jimmyng94/PawBeat/Other/Media/BPM.png

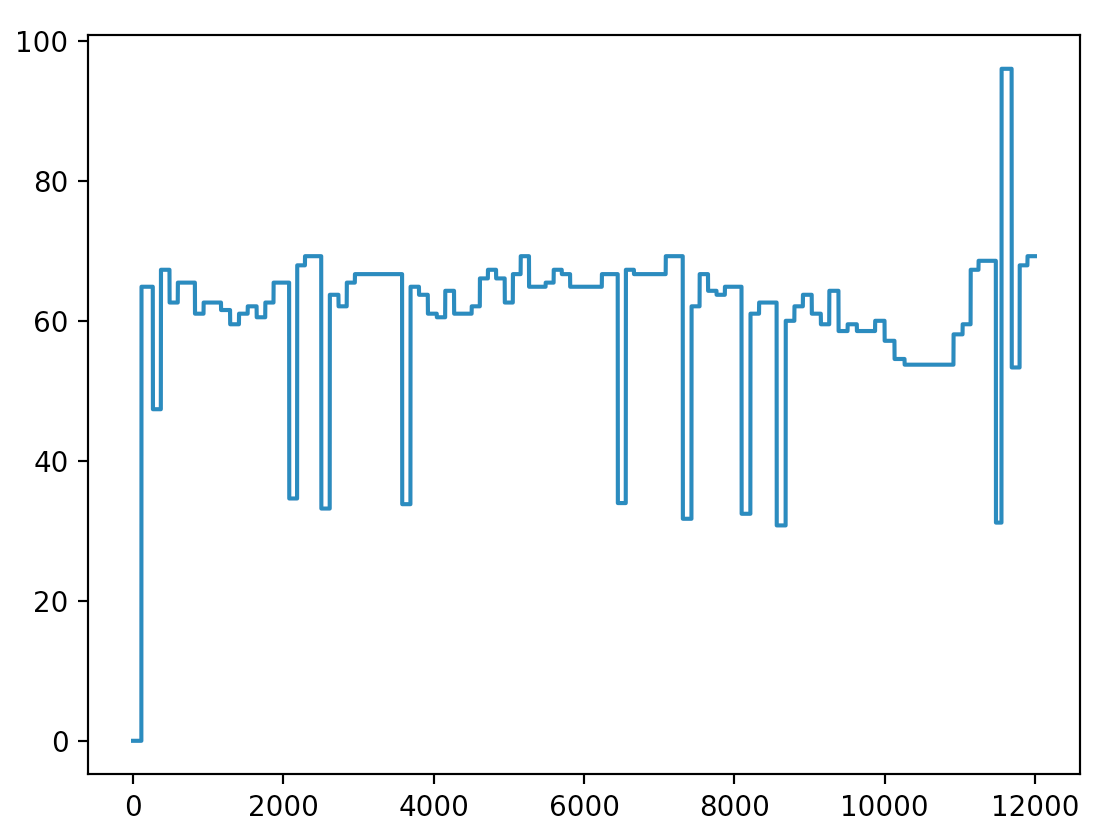
Other/Media/BPM.png
