jimmyng94/PawBeat/Other/Media/Filtered Data.png

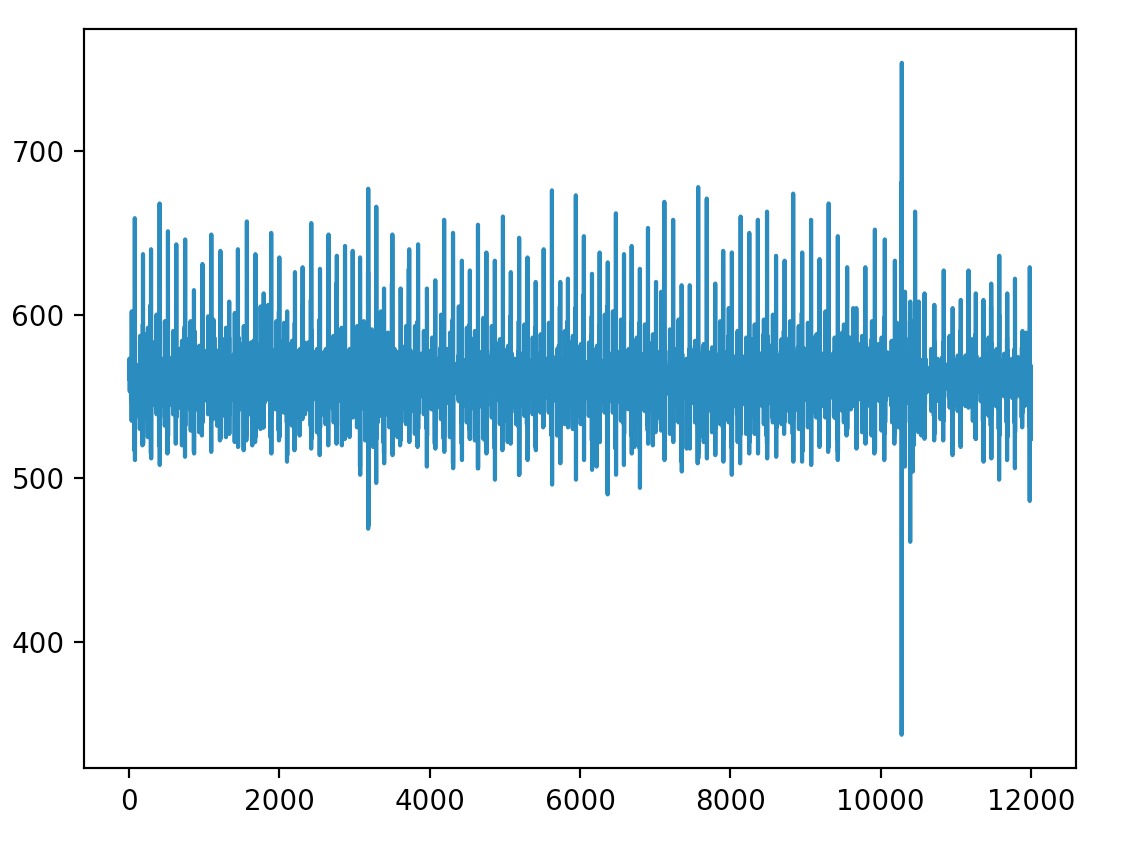
Other/Media/Filtered Data.png
