jimmyng94/PawBeat/Other/Media/Filtered_Zoom.png

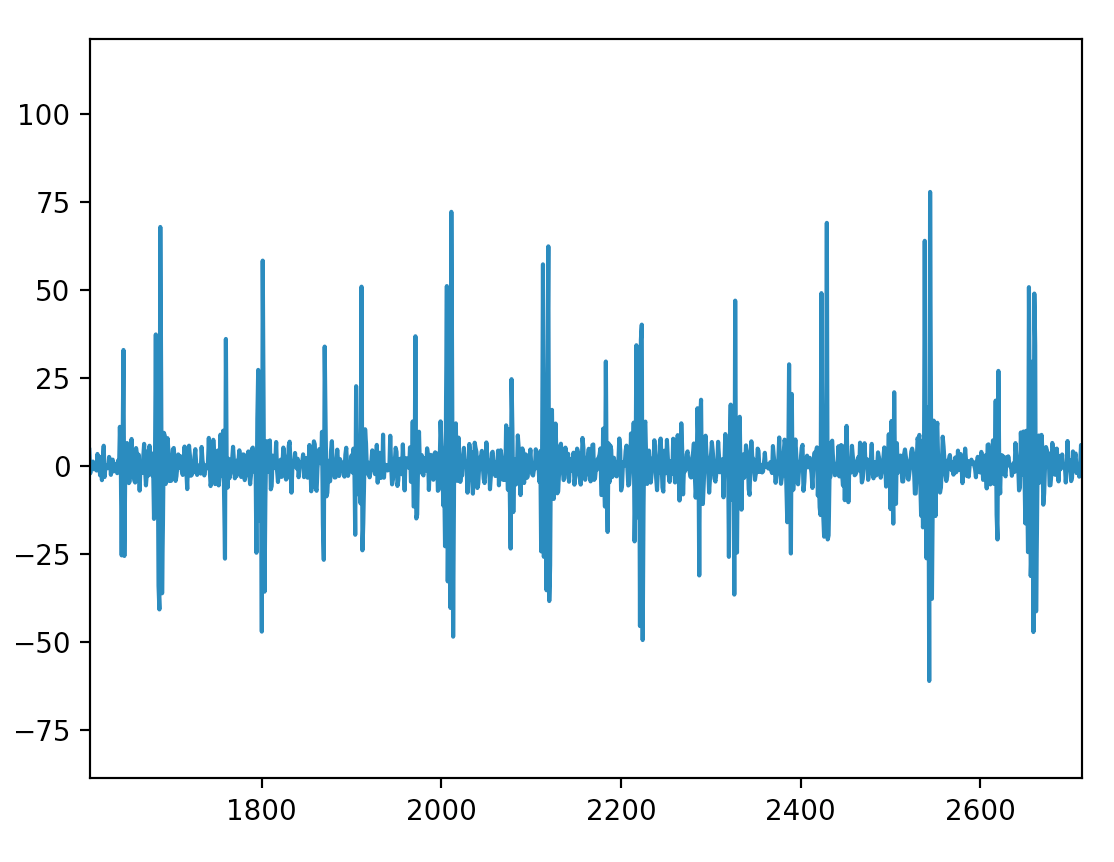
Other/Media/Filtered_Zoom.png
