jimmyng94/PawBeat/Other/Media/image0.jpeg

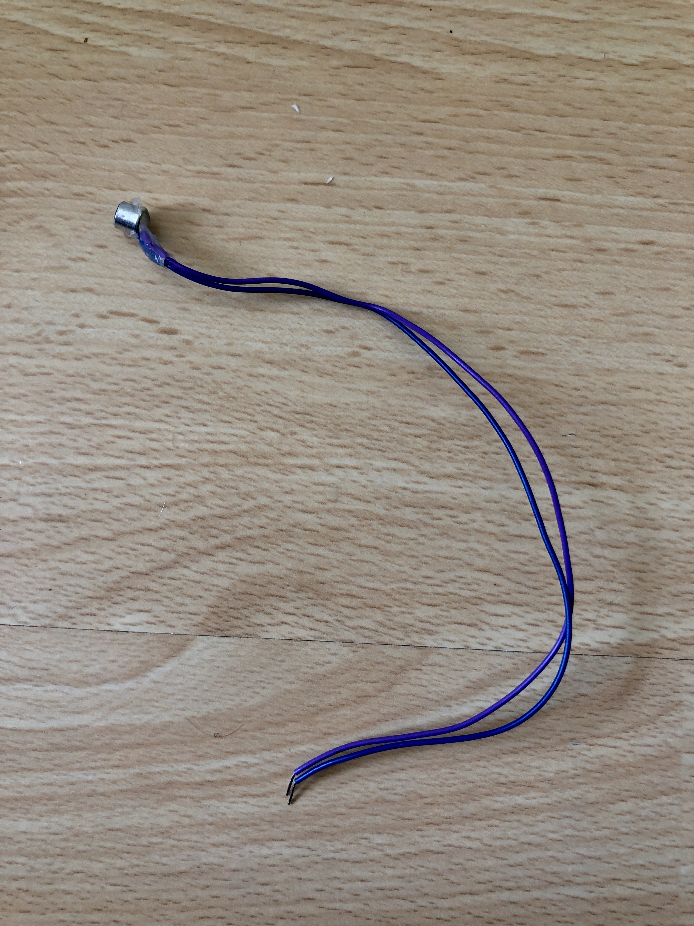
Other/Media/image0.jpeg
