jimmyng94/PawBeat/Other/Media/image1.jpeg

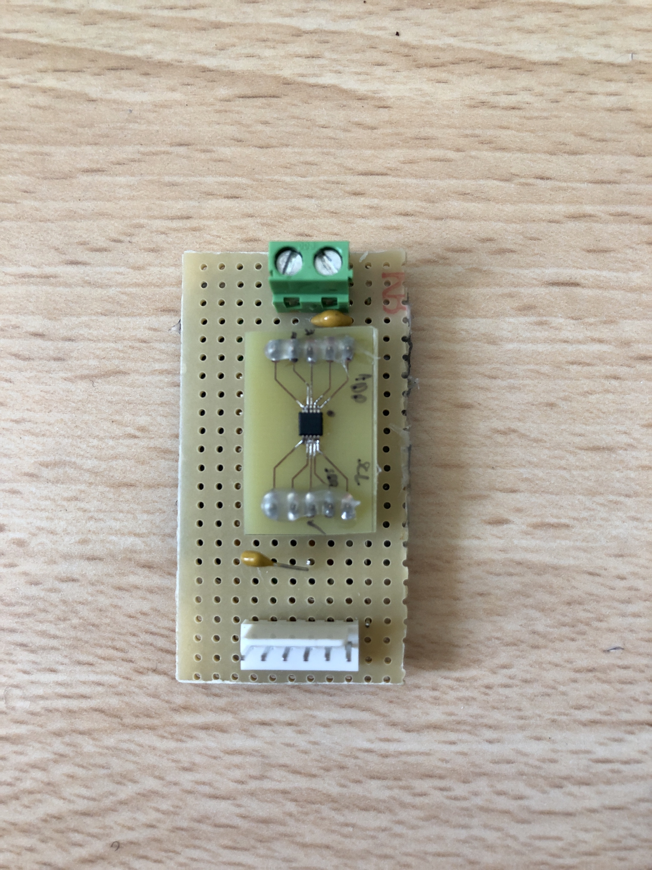
Other/Media/image1.jpeg
