jimmyng94/PawBeat/Other/Media/image3.jpeg

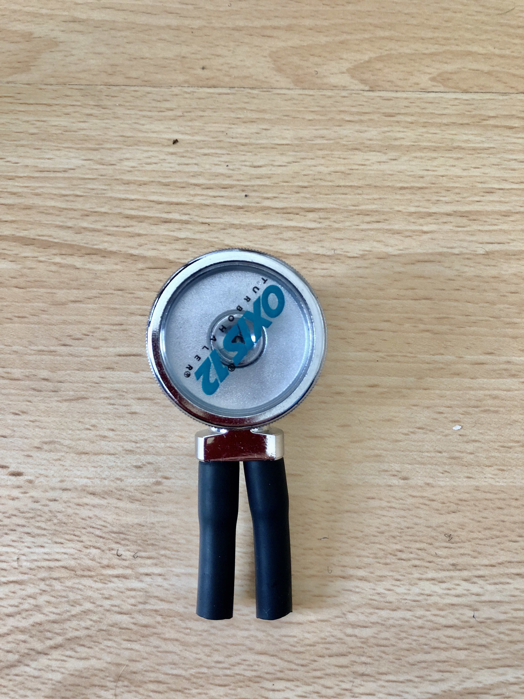
Other/Media/image3.jpeg
