jimmyng94/PawBeat/Other/Media/image4.jpeg

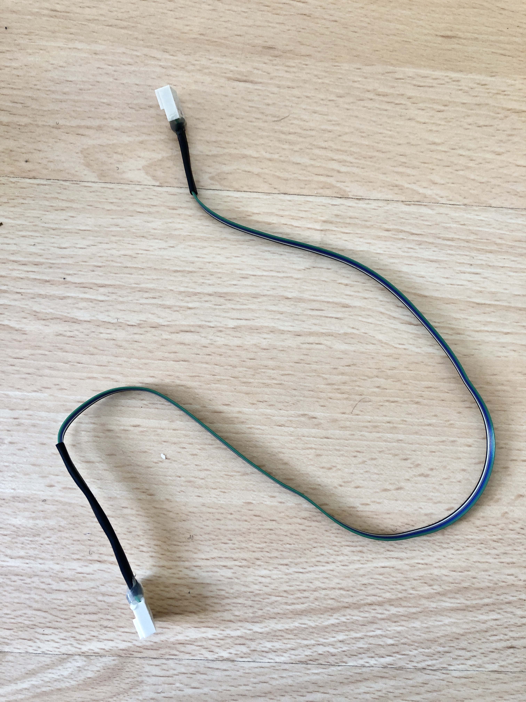
Other/Media/image4.jpeg
