jimmyng94/PawBeat/Other/Media/image5.jpeg

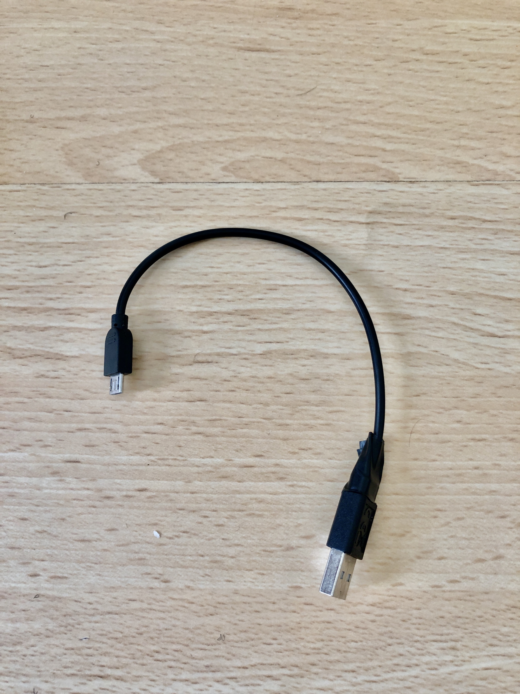
Other/Media/image5.jpeg
