jimmyng94/PawBeat/Other/Media/image6.jpeg

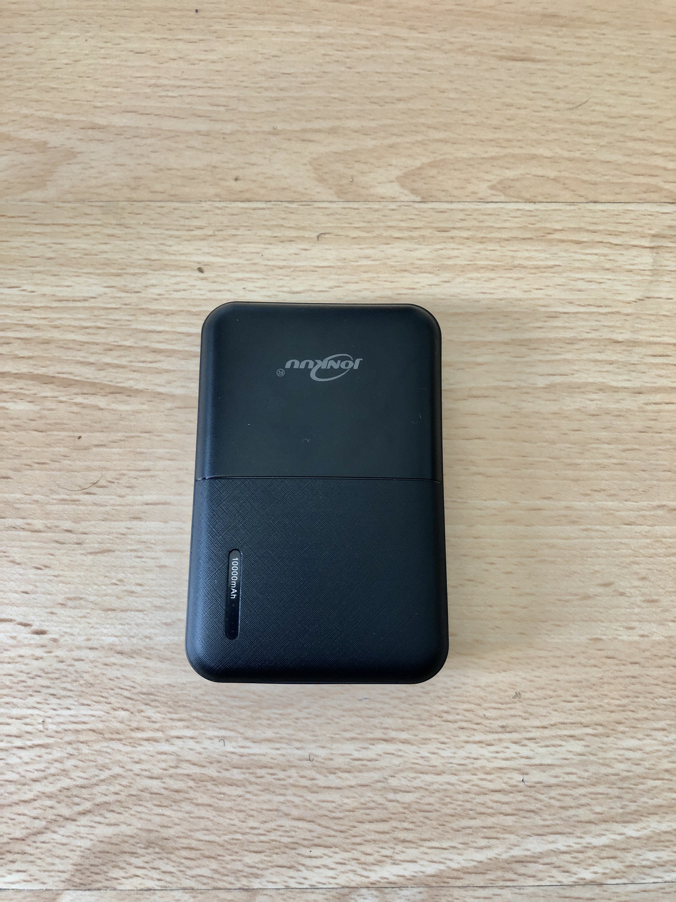
Other/Media/image6.jpeg
