jimmyng94/PawBeat/Other/Media/image7.jpeg

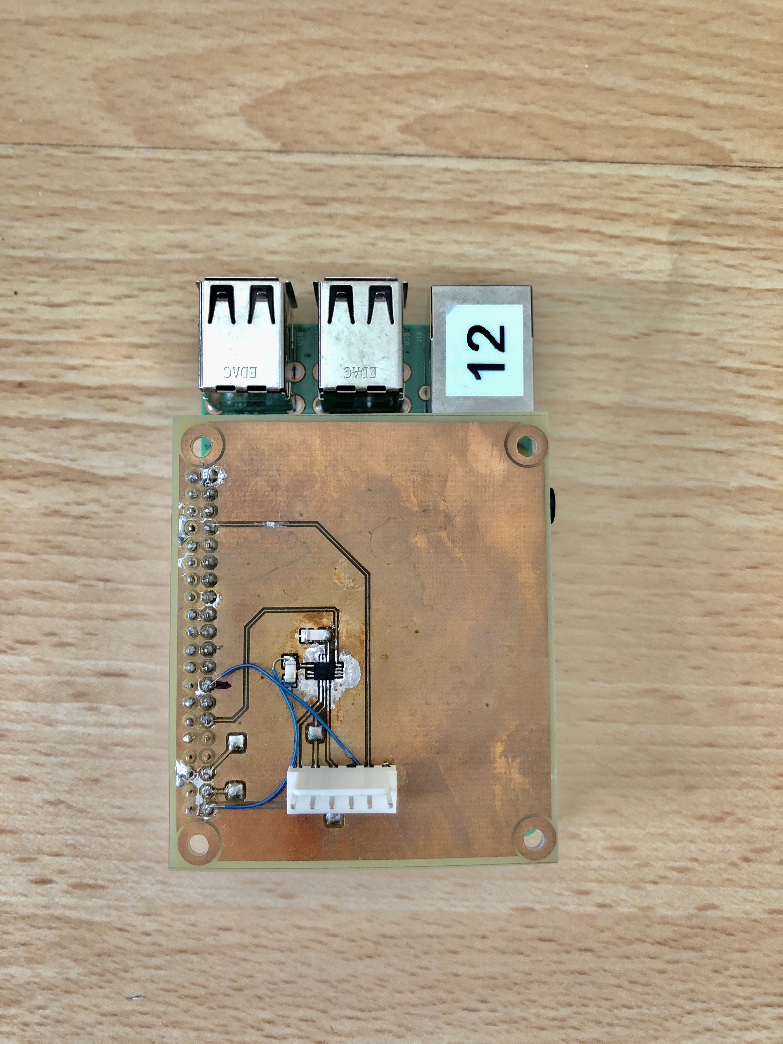
Other/Media/image7.jpeg
