jimmyng94/PawBeat/Other/Media/image9.jpeg

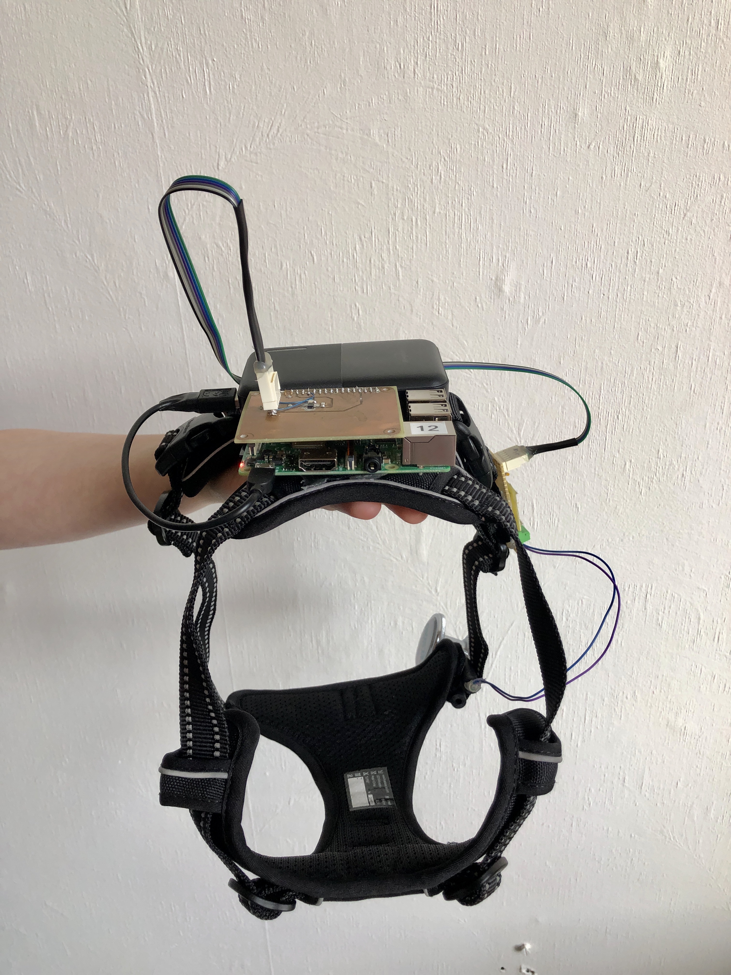
Other/Media/image9.jpeg
