jimmyng94/PawBeat/Other/Media/Initial Data.png

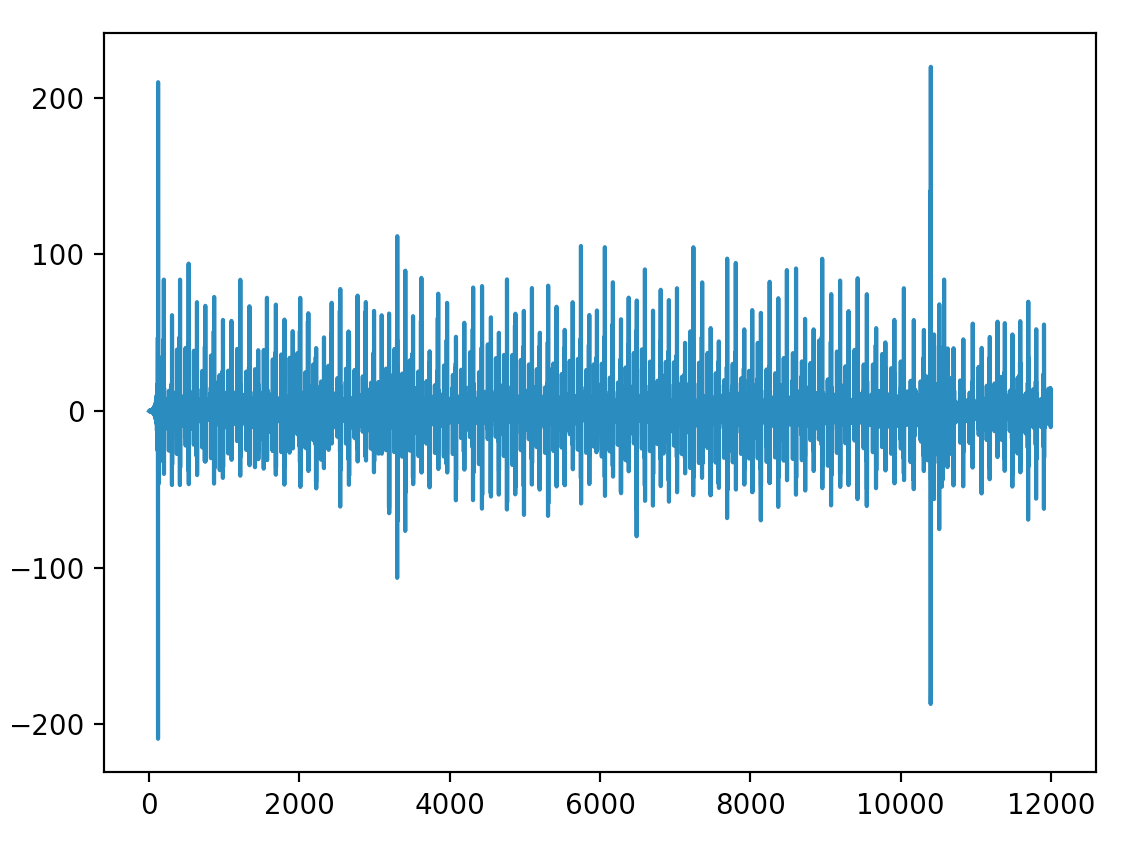
Other/Media/Initial Data.png
