jimmyng94/PawBeat/Other/Media/Squared.png

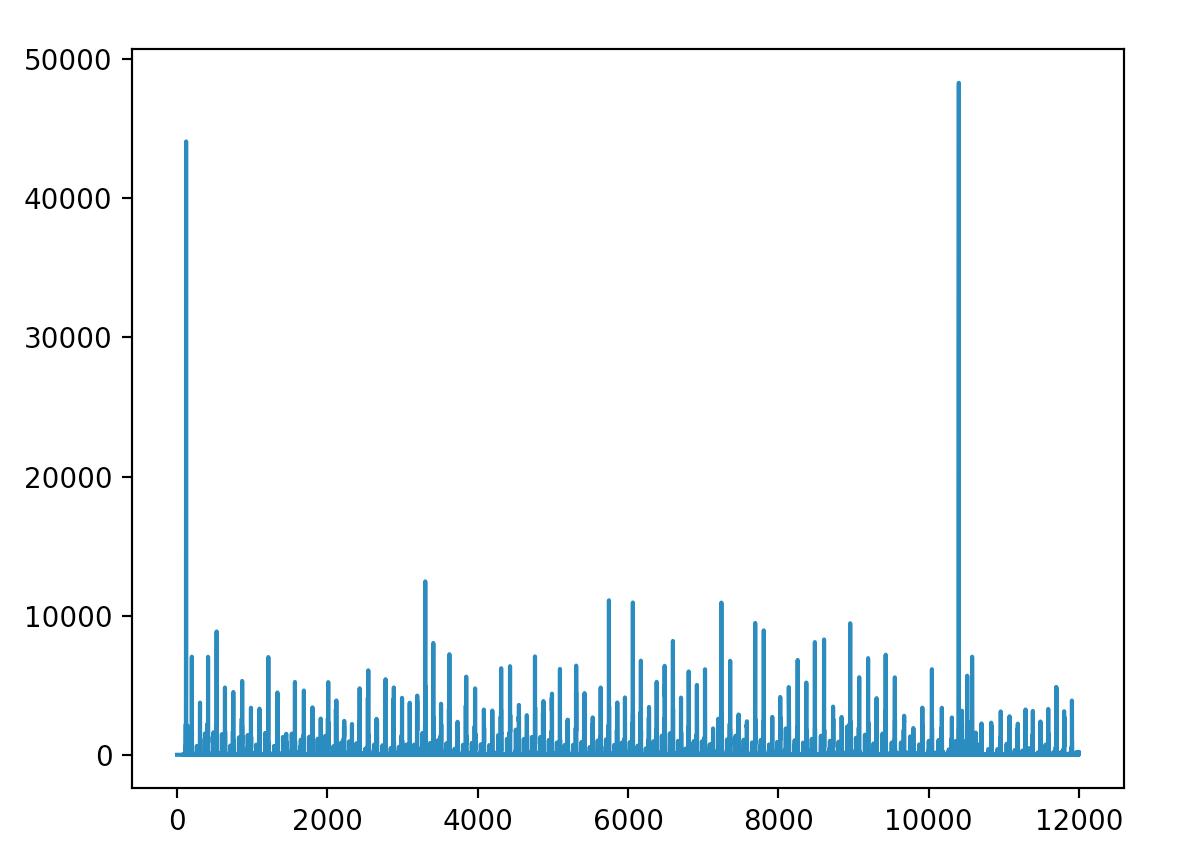
Other/Media/Squared.png
