jimmyng94/PawBeat/Other/Media/Step_Mag.png

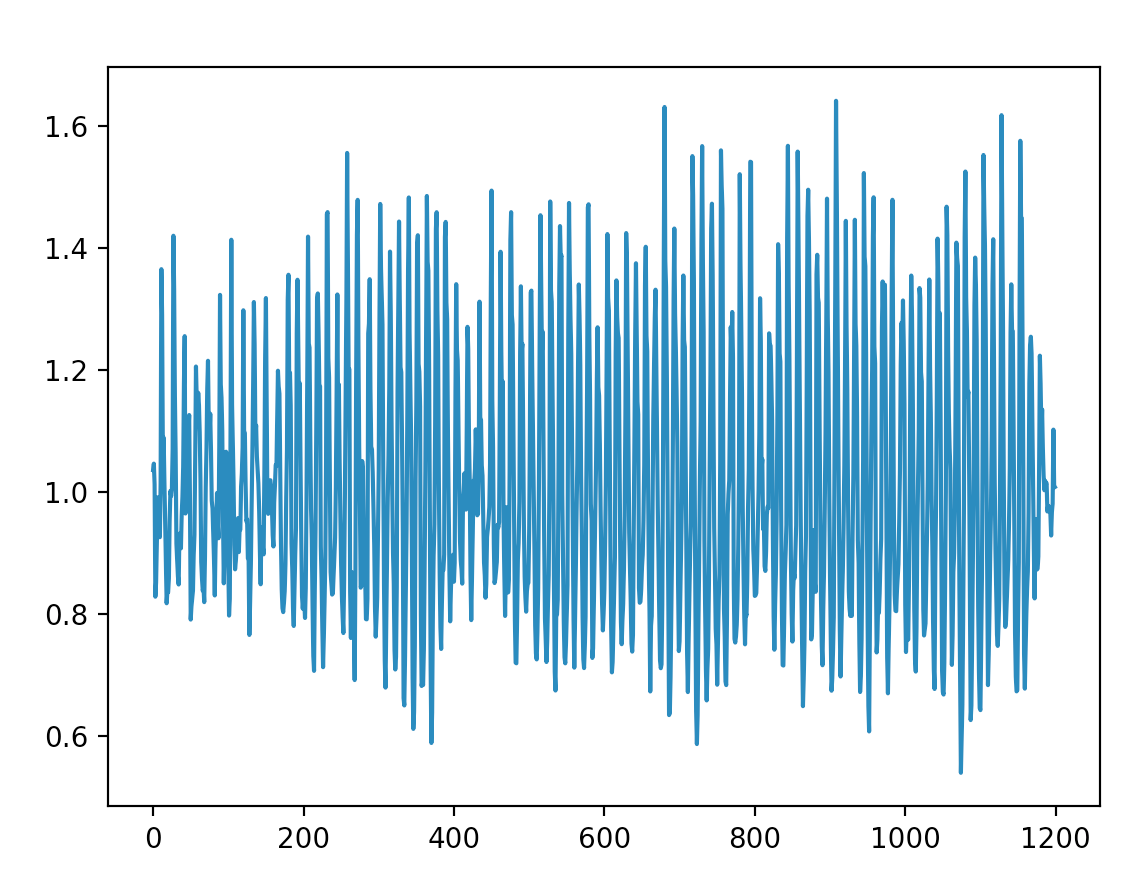
Other/Media/Step_Mag.png
