jimmyng94/PawBeat/Other/Media/Step_Mag_Zoom.png

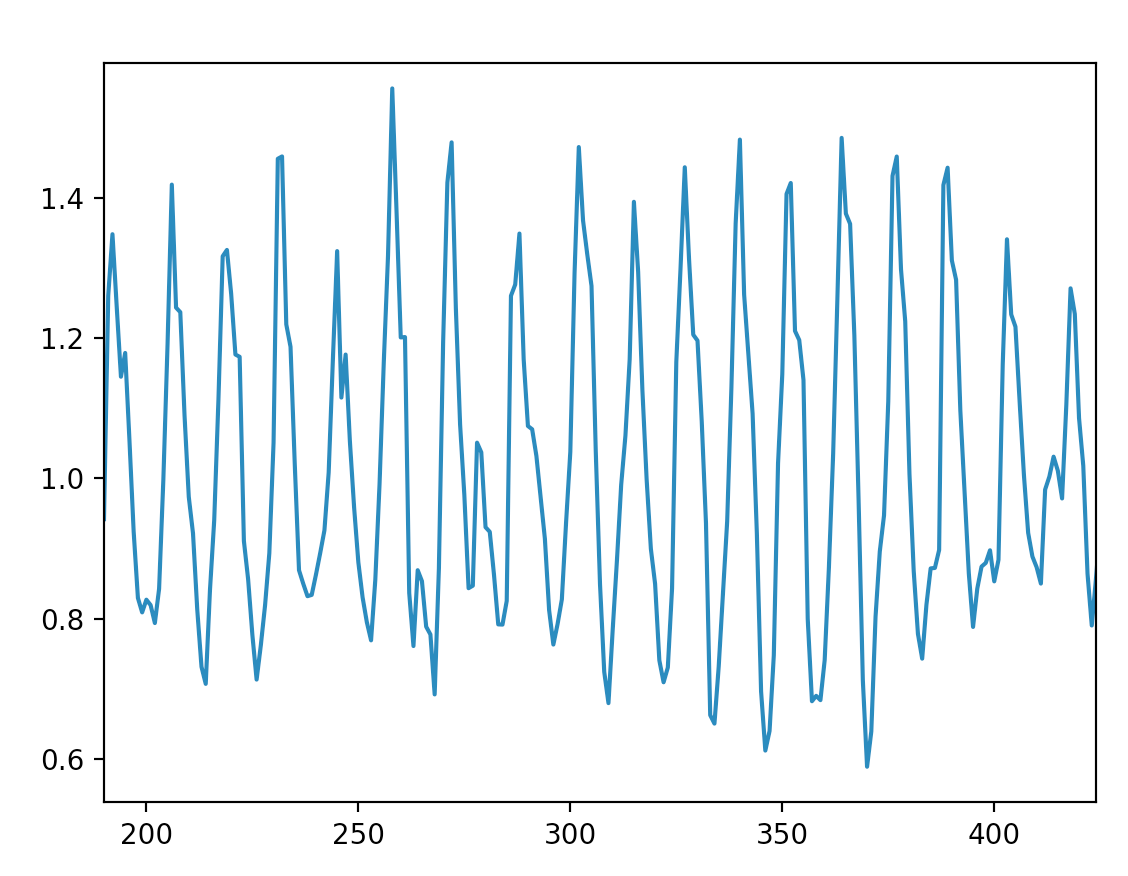
Other/Media/Step_Mag_Zoom.png
